pmvt19/physical_robot/physical_robot/robot/robot_utils.py

import numpy as np
import matplotlib.pyplot as plt

from physical_robot.algorithms.particle_filter import ParticleFilter
from physical_robot.robot import Robot
from physical_robot.robot import PhysicalRobotSpace
from physical_robot.maps import Map
from physical_robot.algorithms.icp import run_icp
from physical_robot.utils import transformation_mat_to_state

from motion_planning.search import PRM
from motion_planning.tools import NumpyState, Path

def is_close(state1, state2, threshold=100):
    return np.linalg.norm(state1[:2] - state2[:2]) < threshold

def localize_robot(robot: Robot, 
                   map: Map, 
                   num_particles: int = 10000, 
                   localizing_motion: str = 'in-place', 
                   custom_localizing_motion: list[tuple] | None = None, 
                   visualize: bool = True) -> tuple[np.ndarray, ParticleFilter]:

    pf = ParticleFilter(map_obj=map)
    pf.initialize(num_particles=num_particles)

    if localizing_motion == 'in-place':
        motion_commands = [['angular', np.pi/2],
                           ['angular', np.pi/2],
                           ['angular', np.pi/2],
                           ['angular', np.pi/2]]
    elif localizing_motion == 'single in-place':
        motion_commands = [['angular', np.pi/2]]
    elif localizing_motion == 'square':
        linear_dist = 10.0
        motion_commands = [['linear', linear_dist],
                           ['angular', np.pi/2],
                           ['linear', linear_dist],
                           ['angular', np.pi/2],
                           ['linear', linear_dist],
                           ['angular', np.pi/2],
                           ['linear', linear_dist],
                           ['angular', np.pi/2],]
    elif localizing_motion == 'custom':
        if custom_localizing_motion:
            motion_commands = custom_localizing_motion
        else:
            raise ValueError('"custom" set for localizing motion but no custom motions was given via the custom_localizing_motion argument')

    for motion_command in motion_commands:
        m = robot.command_motion_trial(motion_command)
        scan, lidar_data = robot.read_lidar_updated(wait_for_updated_reading=True)

        updated_state = pf.step(motion_delta=motion_command, scan=lidar_data)

    if visualize:
        pf.visualize_particles(plt.gca())
        pf.map.visualize_points(plt.gca())
        plt.scatter(updated_state[0], updated_state[1], color='orange', zorder=2)
        plt.show()
    return updated_state, pf

def visualize_prm(robot: PhysicalRobotSpace, prm: PRM, path=None):
    # Draw Path
    robot.map.visualize_points(plt.gca())
    prm.draw(plt.gca(), path=path, show_task=True)
    plt.show()

    # Draw Individual States
    # robot.map.visualize_points(plt.gca())
    # for state in path:
    #     robot.draw_state

def mpc_plan_and_follow_trajectory(robot: PhysicalRobotSpace,
                                   pf: ParticleFilter,
                                   map: Map,
                                   prm: PRM,
                                   start: NumpyState,
                                   target: NumpyState,
                                   visualize_iterative_path: bool = False):

    path = prm.search(start, target)
    visualize_prm(robot, prm, path)
    path = [p.value for p in path]
    current_state = start

    while not is_close(current_state.value, target.value):
        motion_commands = robot.path_to_motion_commands(path)
        
        for i, motion_command in enumerate(motion_commands):
            print(f"Executing Motion Command: {motion_command}")
            m, predicted_state = robot.command_motion_and_predict_state(current_state.value, motion_command)
            
            coords, lidar_data = robot.read_lidar_updated(wait_for_updated_reading=True, manual_verification=False)

            # Particle Filter State Prediction Update
            current_state = pf.step(motion_delta=motion_command, scan=lidar_data)
            print(f"Current State After Particle Filter Update: {np.round(current_state, 2)}")

            # ICP State Refinement
            T = run_icp(coords, map.get_points(), current_state, filter_init_outliers=False, visualize=False)
            current_state = robot.make_state(transformation_mat_to_state(T))
            print(f"Current State After ICP Refinement: {np.round(current_state.value, 2)}")

            # Break to replan if we are on the 4th Motion Command
            if i == 3:
                break
        
        path = prm.search(current_state, target)
        if visualize_iterative_path:
            visualize_prm(robot, prm, path)
        path = [p.value for p in path]
        motion_commands = robot.path_to_motion_commands(path)
            

def path_obj_to_list_of_states(path: Path):
    return [p.value for p in path]
